robotonio/robotonio-Power-Generating-Pavement-Slabs/Project_code/is_night.png

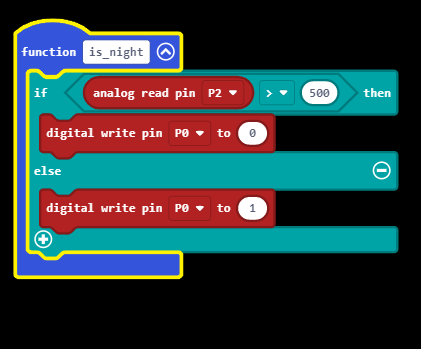
Project_code/is_night.png
