robotonio/robotonio-Power-Generating-Pavement-Slabs/Project_code/main.png

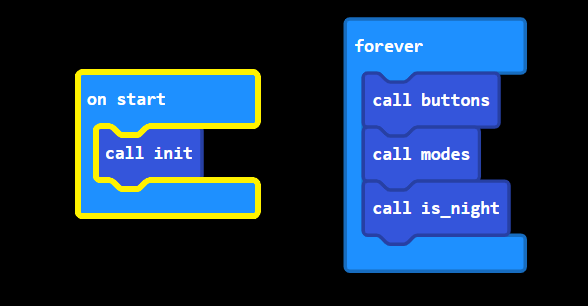
Project_code/main.png
