robotonio/robotonio-Power-Generating-Pavement-Slabs/Project_code/modes.png

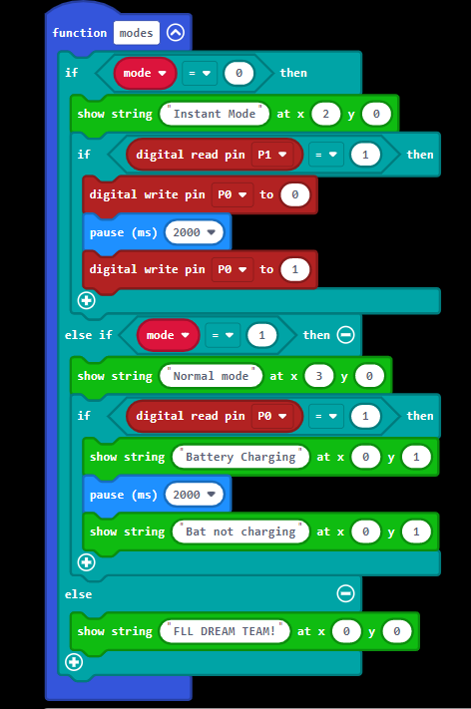
Project_code/modes.png
